petrbrouzda/ina219-esp32-power_meter/ina219_app_wifi_g2/MeteringPageRender.h

void print_dumpValuesToSerial();
void print_page1_half1();
void print_page1_half2();
void print_page2_half1();
void print_page2_half2();
void print_page3_half1();
void print_page3_half2();
void print_page4_half1();
void print_page4_half2();
void print_page5_half1();
void print_page5_half2();
void print_page_footer();
void print_page_footer2( int percent );
